Tomas-Kuchta-FPV/Travel-Buddy/4x3 keyboard/T9_Labels/T9_4.png

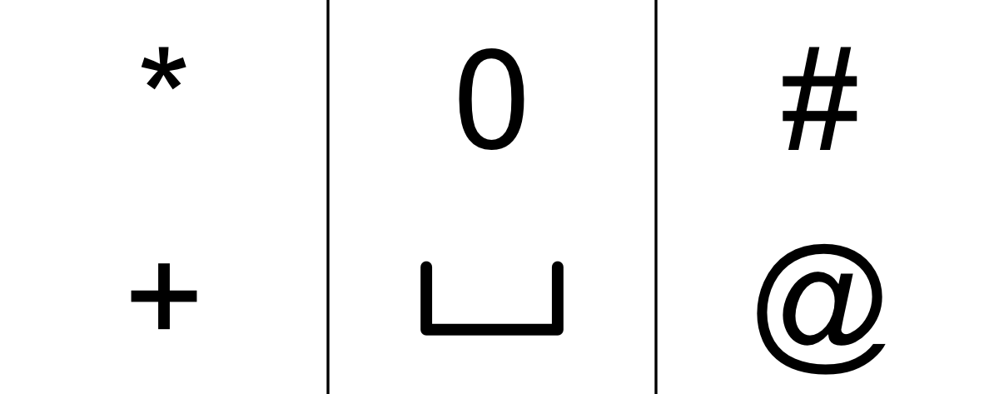
4x3 keyboard/T9_Labels/T9_4.png
