Tomas-Kuchta-FPV/Travel-Buddy/Images/Buttons.png

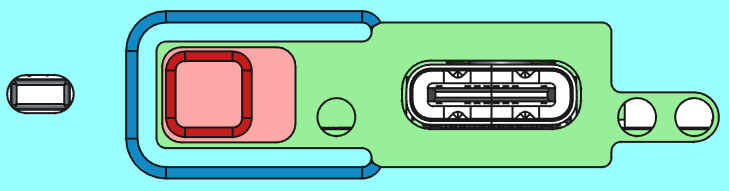
Images/Buttons.png
