Tomas-Kuchta-FPV/Travel-Buddy/Images/Prototype_Front.jpg

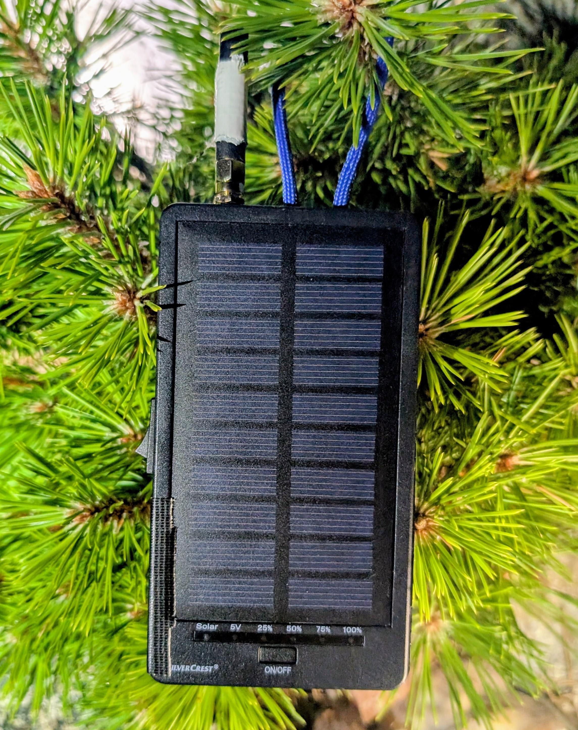
Images/Prototype_Front.jpg
