Tomas-Kuchta-FPV/Travel-Buddy/Images/Screens 2.7.20/1_main.jpg

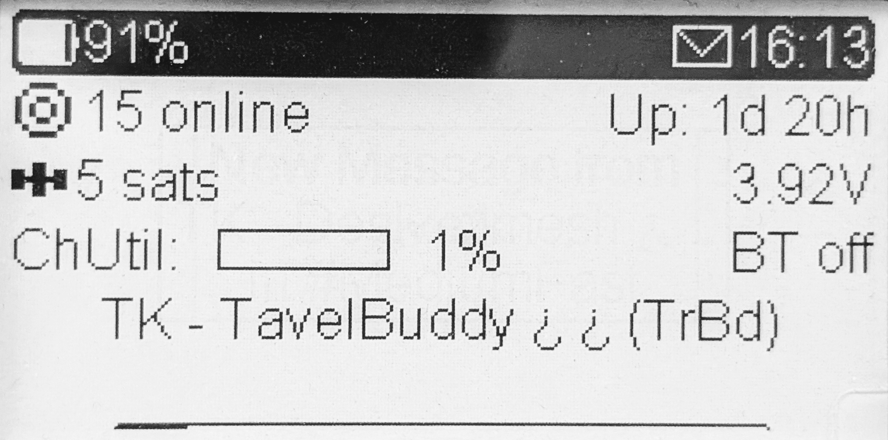
Images/Screens 2.7.20/1_main.jpg
