Tomas-Kuchta-FPV/Travel-Buddy/Images/Screens 2.7.20/2.1_message.jpg

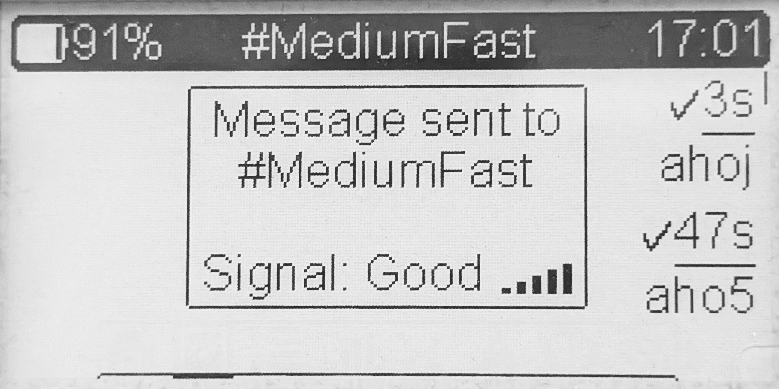
Images/Screens 2.7.20/2.1_message.jpg
