Tomas-Kuchta-FPV/Travel-Buddy/Images/Screens 2.7.20/2.2_message.jpg

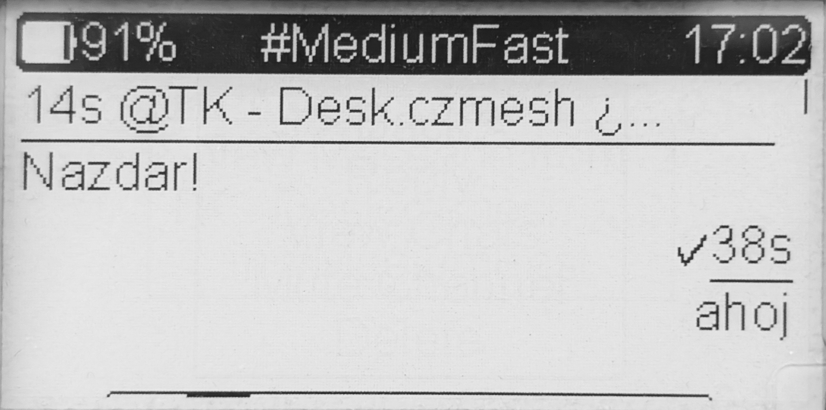
Images/Screens 2.7.20/2.2_message.jpg
