Tomas-Kuchta-FPV/Travel-Buddy/Images/Screens 2.7.20/3_heard.jpg

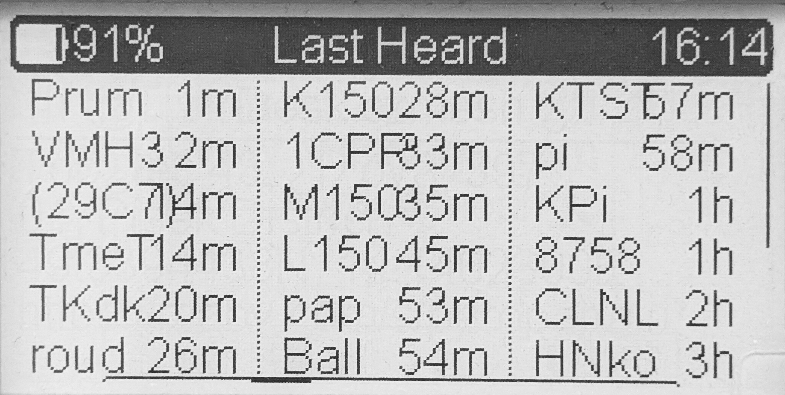
Images/Screens 2.7.20/3_heard.jpg
