Tomas-Kuchta-FPV/Travel-Buddy/Images/Screens 2.7.20/4_hop.jpg

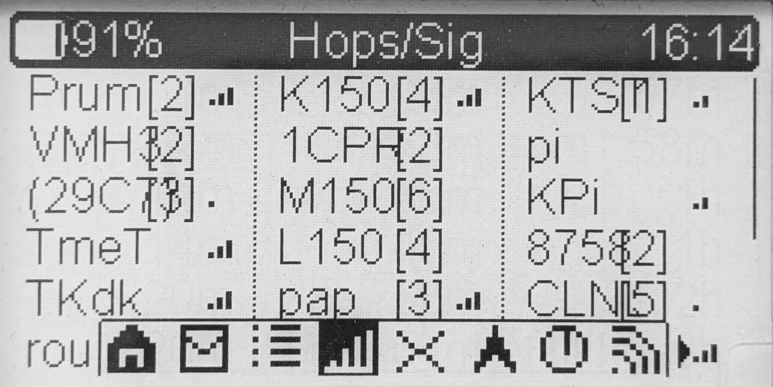
Images/Screens 2.7.20/4_hop.jpg
