Tomas-Kuchta-FPV/Travel-Buddy/Images/Screens 2.7.20/6_bearings.jpg

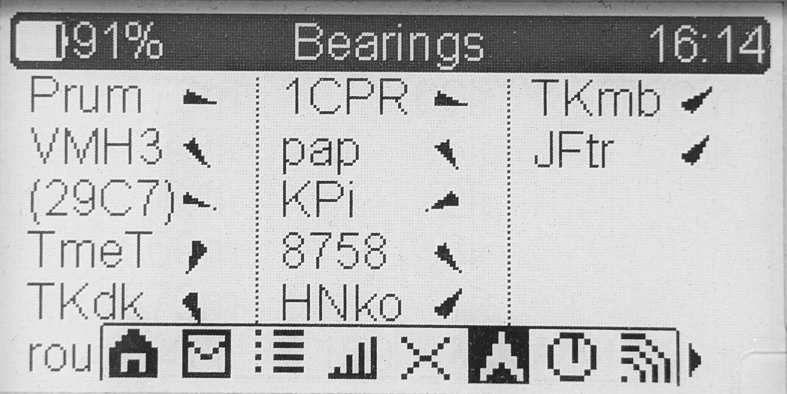
Images/Screens 2.7.20/6_bearings.jpg
