Tomas-Kuchta-FPV/Travel-Buddy/Images/Screens 2.7.20/9_system.jpg

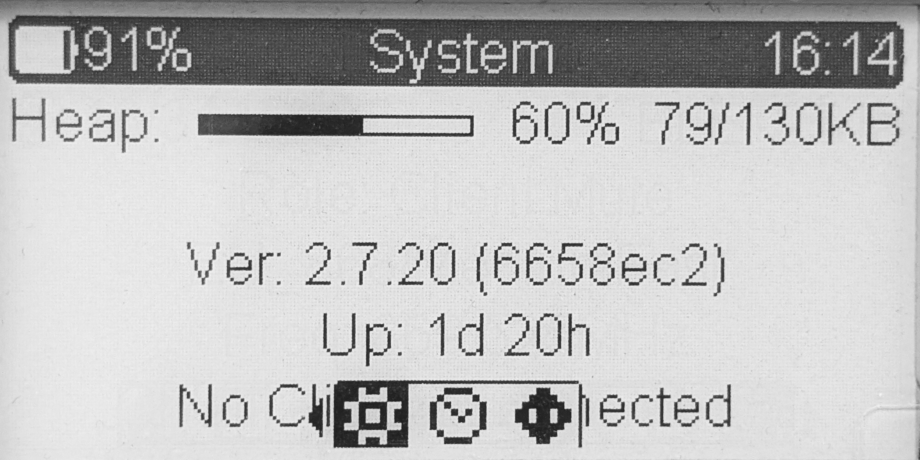
Images/Screens 2.7.20/9_system.jpg
