Tomas-Kuchta-FPV/Travel-Buddy/Images/Screens 2.7.20/10_clock.jpg

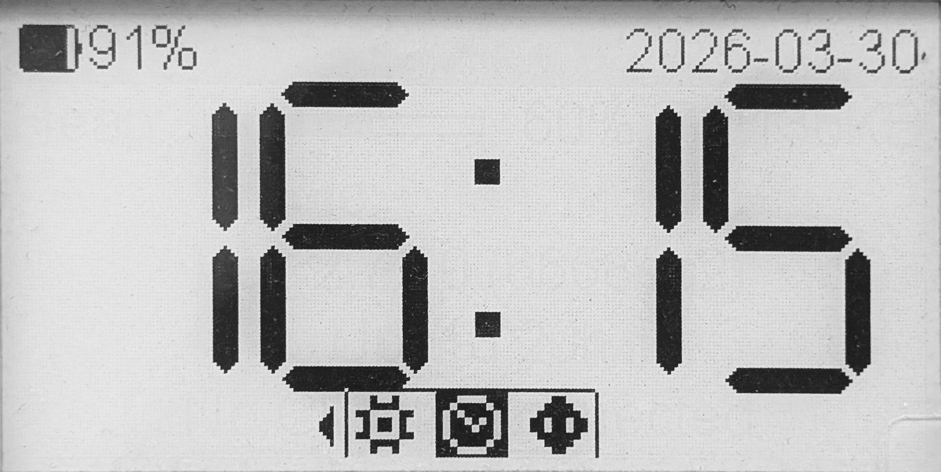
Images/Screens 2.7.20/10_clock.jpg
