Tomas-Kuchta-FPV/Travel-Buddy/Images/Screens 2.7.20/11_enviroment.jpg

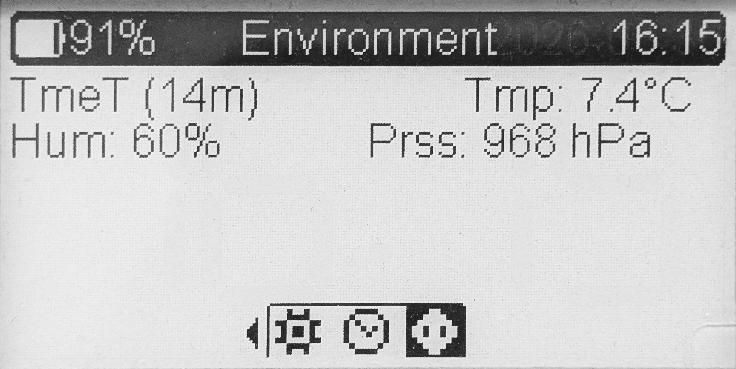
Images/Screens 2.7.20/11_enviroment.jpg
